hatchman/Game-Boy-Camera-Shell/BuildImages/GlamCartFront2.png

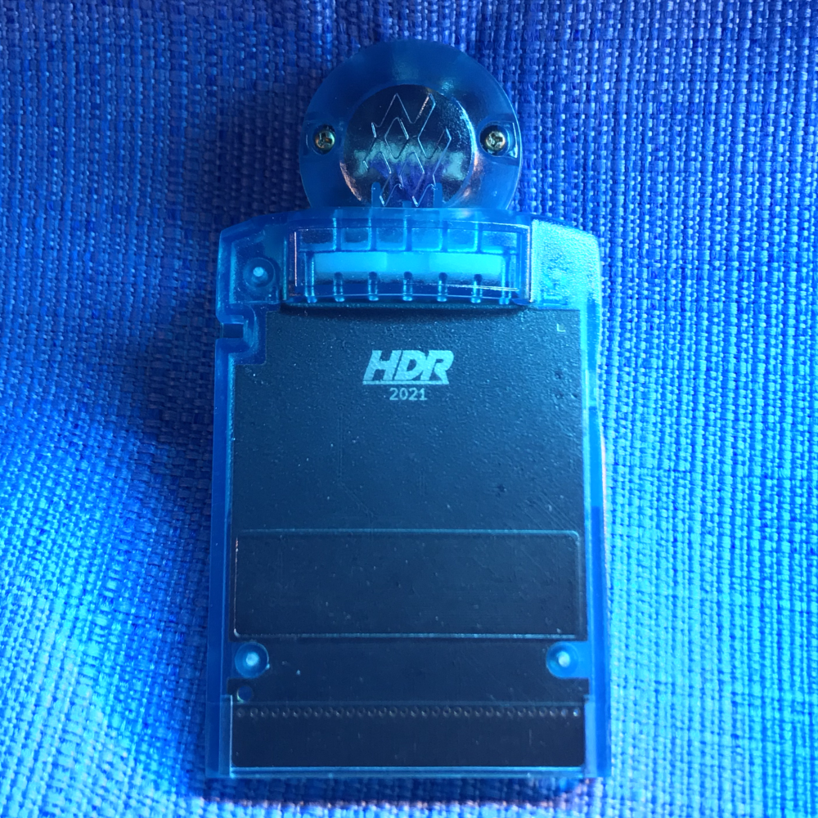
BuildImages/GlamCartFront2.png
