hatchman/Game-Boy-Camera-Shell/BuildImages/GlamOFF.png

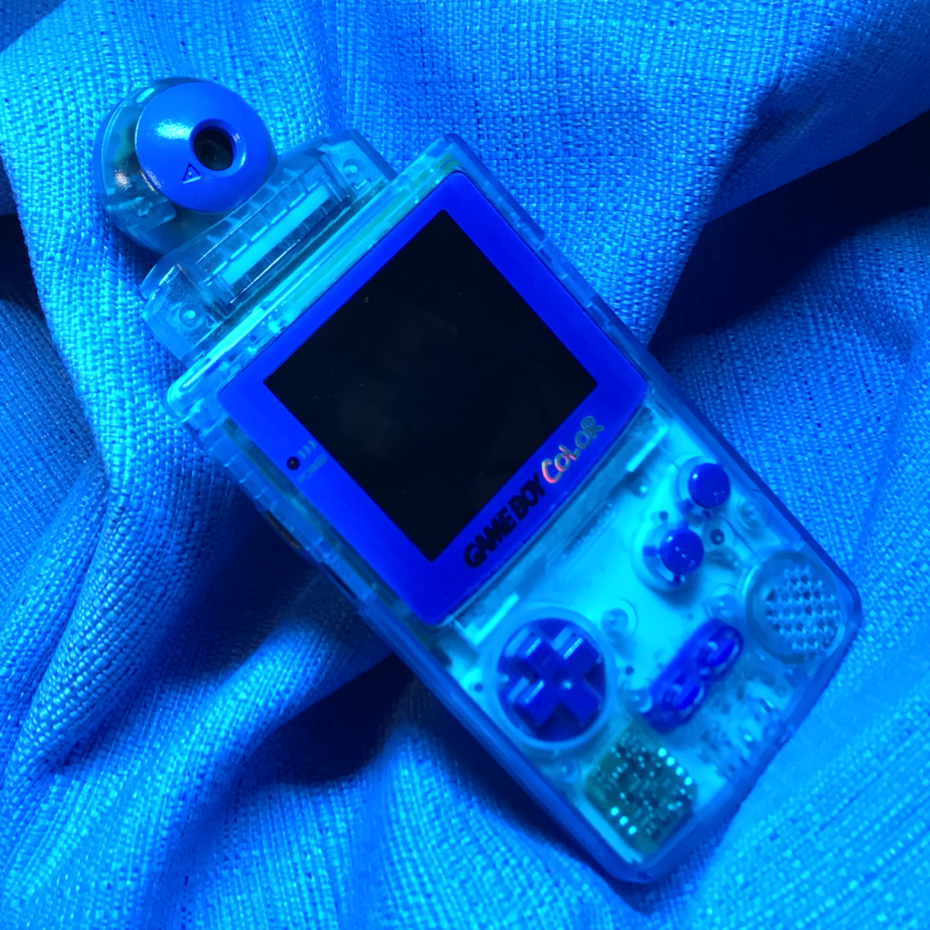
BuildImages/GlamOFF.png
