hatchman/Game-Boy-Camera-Shell/BuildImages/GlamPXLR.png

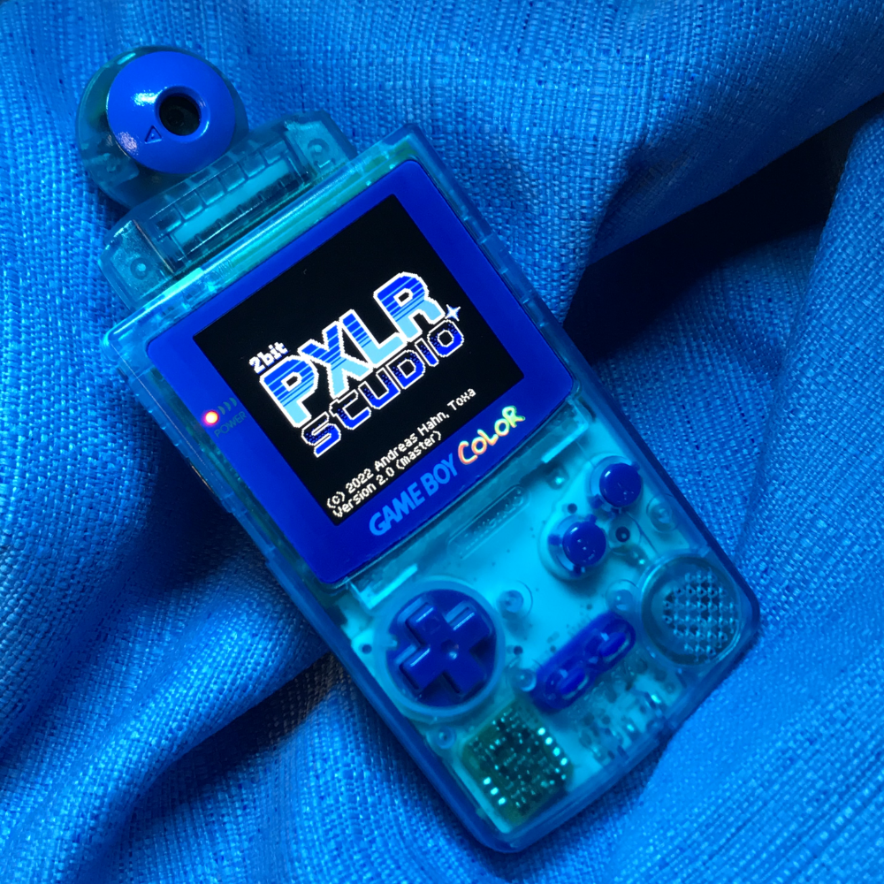
BuildImages/GlamPXLR.png
