hatchman/Game-Boy-Camera-Shell/BuildImages/GlamRear.png

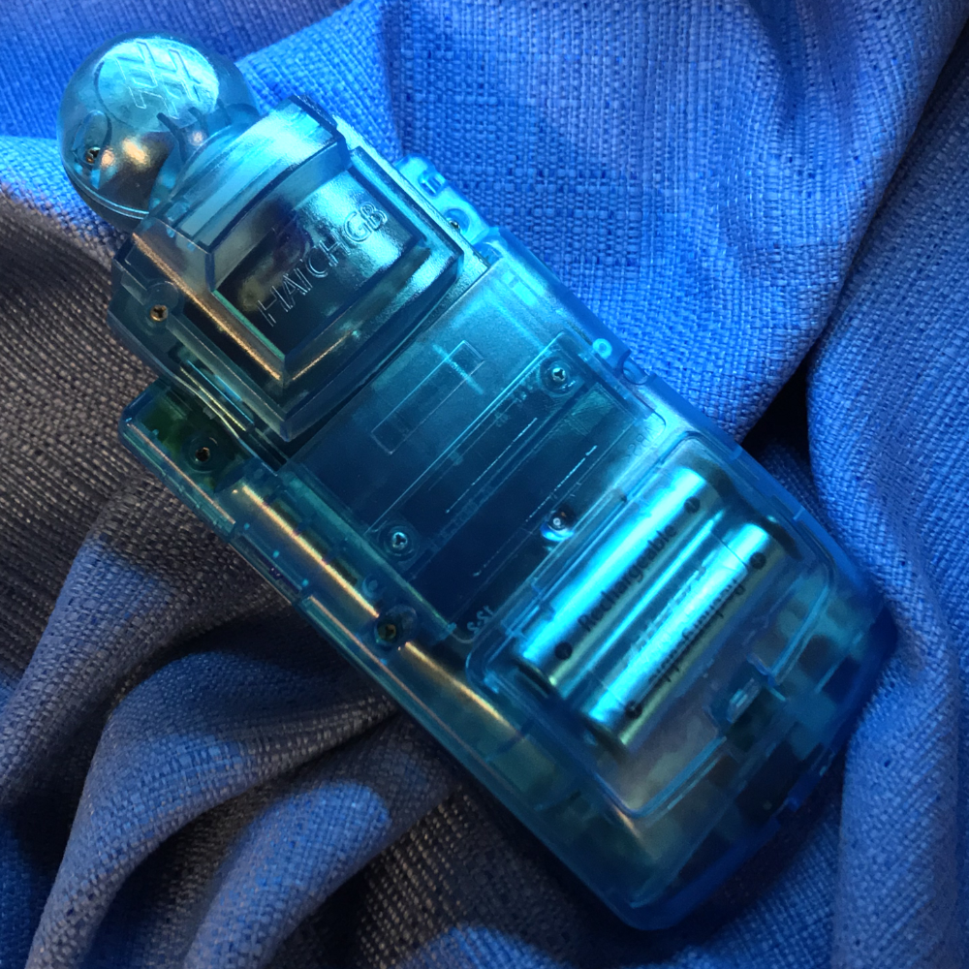
BuildImages/GlamRear.png
