hatchman/Game-Boy-Camera-Shell/BuildImages/SideSwitch.png

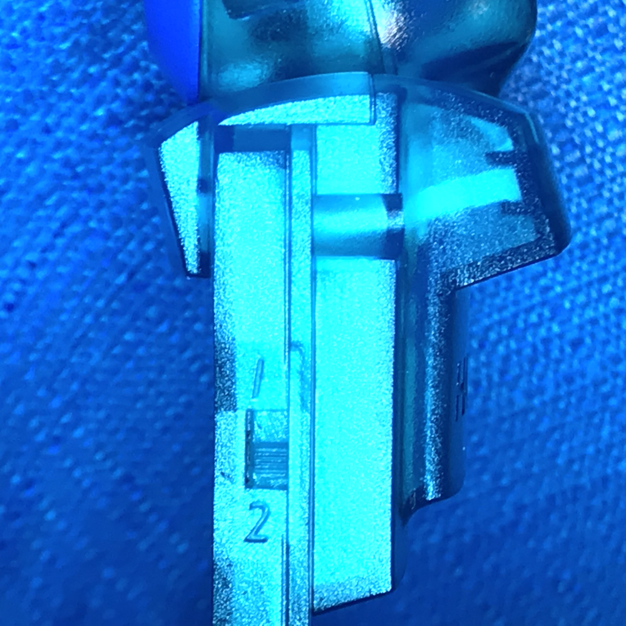
BuildImages/SideSwitch.png
